J-Jaywalker/BeyMeter/src/bb_font.h

#pragma once
#include <stdint.h>

// bb_loading_font.ttf  size=12  cell_h=13
#define BFONT_H 13

static const uint8_t bfont_widths[95] = {
    6, 5, 7, 10, 10, 10, 10, 5, 6, 6, 6, 6, 3, 6, 3, 10, 10, 5, 9, 9, 10, 10, 10, 9, 10, 10, 4, 4, 7, 7, 6, 9, 10, 9, 9, 10, 10, 9, 9, 10, 9, 9, 8, 9, 7, 11, 9, 10, 9, 10, 9, 10, 9, 10, 11, 15, 10, 10, 9, 6, 8, 6, 10, 6, 4, 10, 9, 10, 10, 9, 9, 10, 10, 5, 8, 9, 7, 14, 9, 10, 9, 10, 9, 10, 9, 10, 11, 15, 10, 10, 9, 6, 5, 6, 7
};

static const uint16_t bfont_offsets[95] = {
    0, 12, 22, 36, 56, 76, 96, 116, 126, 138, 150, 162, 174, 180, 192, 198, 218, 238, 248, 266, 284, 304, 324, 344, 362, 382, 402, 410, 418, 432, 446, 458, 476, 496, 514, 532, 552, 572, 590, 608, 628, 646, 664, 680, 698, 712, 734, 752, 772, 790, 810, 828, 848, 866, 886, 908, 938, 958, 978, 996, 1008, 1024, 1036, 1056, 1068, 1076, 1096, 1114, 1134, 1154, 1172, 1190, 1210, 1230, 1240, 1256, 1274, 1288, 1316, 1334, 1354, 1372, 1392, 1410, 1430, 1448, 1468, 1490, 1520, 1540, 1560, 1578, 1590, 1600, 1612
};

static const uint8_t bfont_data[1626] = {
    0x00, 0x00, 0x00, 0x00, 0x00, 0x00, 0x00, 0x00, 0x00, 0x00, 0x00, 0x00, 0x00, 0x00, 0x03, 0x40,
    0x1F, 0x40, 0x1C, 0x00, 0x00, 0x00, 0x00, 0x00, 0x00, 0x00, 0x18, 0x00, 0x10, 0x00, 0x18, 0x00,
    0x18, 0x00, 0x00, 0x00, 0x00, 0x00, 0x01, 0x00, 0x05, 0xC0, 0x1F, 0xC0, 0x1F, 0x00, 0x05, 0xC0,
    0x0F, 0xC0, 0x1F, 0x00, 0x1D, 0x00, 0x00, 0x00, 0x00, 0x00, 0x00, 0x40, 0x0E, 0x40, 0x1E, 0xF0,
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
    0x00, 0x00, 0x03, 0x80, 0x0F, 0xC0, 0x1C, 0xC0, 0x1A, 0x40, 0x12, 0x40, 0x12, 0xC0, 0x13, 0xC0,
    0x13, 0x00, 0x00, 0x00, 0x00, 0x40, 0x07, 0xC0, 0x1F, 0xC0, 0x1E, 0x00, 0x02, 0x00, 0x02, 0xC0,
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
};
